chaos-adept/iot-dipstick/arduino/air-monitor/src/yandex_cloud_mqtt_settings.h

const char* mqttserver = "130.193.44.244"; //mqtt.cloud.yandex.net
const int mqttport=8883;

const int mqttKeepAlive = 10 * 1000;
const int mqttBufferSize = 1024;

const char* registry_root_ca = \
"-----BEGIN CERTIFICATE-----\n \
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
LpuQKbSbIERsmR+QqQ==\
-----END CERTIFICATE-----\n";
