chaos-adept/iot-dipstick/arduino/experements/sensors-sgp30-bme680/sensors-sgp30-bme680-test/sensors-sgp30-bme680-test.ino

/***************************************************************************
  This is a library for the BME680 gas, humidity, temperature & pressure sensor

  Designed specifically to work with the Adafruit BME680 Breakout
  ----> http://www.adafruit.com/products/3660

  These sensors use I2C or SPI to communicate, 2 or 4 pins are required
  to interface.

  Adafruit invests time and resources providing this open source code,
  please support Adafruit and open-source hardware by purchasing products
  from Adafruit!

  Written by Limor Fried & Kevin Townsend for Adafruit Industries.
  BSD license, all text above must be included in any redistribution
 ***************************************************************************/

#include <Wire.h>
#include <SPI.h>
#include <Adafruit_Sensor.h>
#include "Adafruit_BME680.h"
#include "Adafruit_SGP30.h"

#define BME_SCK 13
#define BME_MISO 12
#define BME_MOSI 11
#define BME_CS 10

#define SEALEVELPRESSURE_HPA (1013.25)

Adafruit_BME680 bme; // I2C
Adafruit_SGP30 sgp;
//Adafruit_BME680 bme(BME_CS); // hardware SPI
//Adafruit_BME680 bme(BME_CS, BME_MOSI, BME_MISO,  BME_SCK);


/* return absolute humidity [mg/m^3] with approximation formula
* @param temperature [°C]
* @param humidity [%RH]
*/
uint32_t getAbsoluteHumidity(float temperature, float humidity) {
    // approximation formula from Sensirion SGP30 Driver Integration chapter 3.15
    const float absoluteHumidity = 216.7f * ((humidity / 100.0f) * 6.112f * exp((17.62f * temperature) / (243.12f + temperature)) / (273.15f + temperature)); // [g/m^3]
    const uint32_t absoluteHumidityScaled = static_cast<uint32_t>(1000.0f * absoluteHumidity); // [mg/m^3]
    return absoluteHumidityScaled;
}

void setup() {
  Serial.begin(115200);
  
  while (!Serial);

  // BME
  
  Serial.println(F("BME680 test"));

  if (!bme.begin()) {
    Serial.println("Could not find a valid BME680 sensor, check wiring!");
    //while (1);
  }

  // Set up oversampling and filter initialization
  bme.setTemperatureOversampling(BME680_OS_8X);
  bme.setHumidityOversampling(BME680_OS_2X);
  bme.setPressureOversampling(BME680_OS_4X);
  bme.setIIRFilterSize(BME680_FILTER_SIZE_3);
  bme.setGasHeater(320, 150); // 320*C for 150 ms


  // SGP30
  
  //while (!Serial) { delay(10); } // Wait for serial console to open!

  Serial.println("SGP30 test");

  if (! sgp.begin()){
    Serial.println("Sensor not found :(");
    while (1);
  }
  Serial.print("Found SGP30 serial #");
  Serial.print(sgp.serialnumber[0], HEX);
  Serial.print(sgp.serialnumber[1], HEX);
  Serial.println(sgp.serialnumber[2], HEX);

  // If you have a baseline measurement from before you can assign it to start, to 'self-calibrate'
  //sgp.setIAQBaseline(0x8E68, 0x8F41);  // Will vary for each sensor!
  //sgp.setIAQBaseline(0xFF26, 0xDB74);  // Will vary for each sensor! -- actual values  
}

int counter = 0;
void loop() {

  // bme680
  
  if (! bme.performReading()) {
    Serial.println("Failed to perform reading from bme680");
    //return;
  }

  
  Serial.println("BME680 results:");
  Serial.print("Temperature = ");
  Serial.print(bme.temperature);
  Serial.println(" *C");

  Serial.print("Pressure = ");
  Serial.print(bme.pressure / 100.0);
  Serial.println(" hPa");

  Serial.print("Humidity = ");
  Serial.print(bme.humidity);
  Serial.println(" %");

  Serial.print("Gas = ");
  Serial.print(bme.gas_resistance / 1000.0);
  Serial.println(" KOhms");

  Serial.print("Approx. Altitude = ");
  Serial.print(bme.readAltitude(SEALEVELPRESSURE_HPA));
  Serial.println(" m");

  Serial.println();


  //SGP30
  
  Serial.println("SGP30 results:");

  //sgp.setHumidity(getAbsoluteHumidity(bme.temperature, bme.humidity));

  if (! sgp.IAQmeasure()) {
    Serial.println("Measurement failed");
    //return;
  }
  Serial.print("TVOC "); Serial.print(sgp.TVOC); Serial.print(" ppb\t");
  Serial.print("eCO2 "); Serial.print(sgp.eCO2); Serial.println(" ppm");

  if (! sgp.IAQmeasureRaw()) {
    Serial.println("Raw Measurement failed");
    //return;
  }
  Serial.print("Raw H2 "); Serial.print(sgp.rawH2); Serial.print(" \t");
  Serial.print("Raw Ethanol "); Serial.print(sgp.rawEthanol); Serial.println("");
 
  delay(1000);

  counter++;
  if (counter == 30) {
    counter = 0;

    uint16_t TVOC_base, eCO2_base;
    if (! sgp.getIAQBaseline(&eCO2_base, &TVOC_base)) {
      Serial.println("Failed to get baseline readings");
      return;
    }
    Serial.print("****Baseline values: eCO2: 0x"); Serial.print(eCO2_base, HEX);
    Serial.print(" & TVOC: 0x"); Serial.println(TVOC_base, HEX);
  }

  Serial.println("read counter:");
  Serial.println(counter);
  
  delay(1000);
}
