chaos-adept/iot-dipstick/arduino/air-monitor/src/time_utils.cpp

#include "time_utils.h"

String getFormattedTime(unsigned long rawTime) {
  unsigned long hours = (rawTime % 86400L) / 3600;
  String hoursStr = hours < 10 ? "0" + String(hours) : String(hours);

  unsigned long minutes = (rawTime % 3600) / 60;
  String minuteStr = minutes < 10 ? "0" + String(minutes) : String(minutes);

  unsigned long seconds = rawTime % 60;
  String secondStr = seconds < 10 ? "0" + String(seconds) : String(seconds);

  return hoursStr + ":" + minuteStr + ":" + secondStr;
}


#define LEAP_YEAR(Y)     ( (Y>0) && !(Y%4) && ( (Y%100) || !(Y%400) ) )

// Based on https://github.com/PaulStoffregen/Time/blob/master/Time.cpp
// currently assumes UTC timezone, instead of using this->_timeOffset
String getFormattedDate(unsigned long secs) {
  unsigned long rawTime = (secs) / 86400L;  // in days
  unsigned long days = 0, year = 1970;
  uint8_t month;
  static const uint8_t monthDays[]={31,28,31,30,31,30,31,31,30,31,30,31};

  while((days += (LEAP_YEAR(year) ? 366 : 365)) <= rawTime)
    year++;
  rawTime -= days - (LEAP_YEAR(year) ? 366 : 365); // now it is days in this year, starting at 0
  days=0;
  for (month=0; month<12; month++) {
    uint8_t monthLength;
    if (month==1) { // february
      monthLength = LEAP_YEAR(year) ? 29 : 28;
    } else {
      monthLength = monthDays[month];
    }
    if (rawTime < monthLength) break;
    rawTime -= monthLength;
  }
  String monthStr = ++month < 10 ? "0" + String(month) : String(month); // jan is month 1  
  String dayStr = ++rawTime < 10 ? "0" + String(rawTime) : String(rawTime); // day of month  
  return String(year) + "-" + monthStr + "-" + dayStr + "T" + getFormattedTime(secs ? secs : 0) + "Z";
}
